BEANS024/Item-Speed-Control-in-Conveyor-Systems-/3D Printed Conveyor/STL Files/Motor Prime Mover Key couple.STL

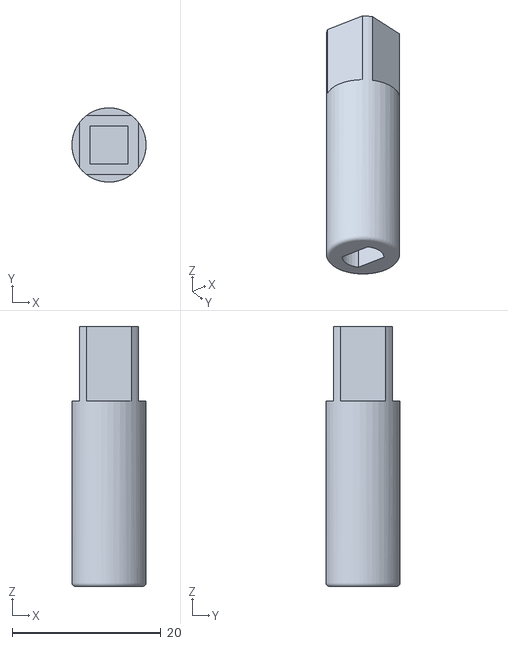
[picture p59: CAD file, 2026-04-25]
3D Printed Conveyor/STL Files/Motor Prime Mover Key couple.STL
10.0 x 10.00 x 35.0
