BEANS024/Item-Speed-Control-in-Conveyor-Systems-/sensor mount.STL

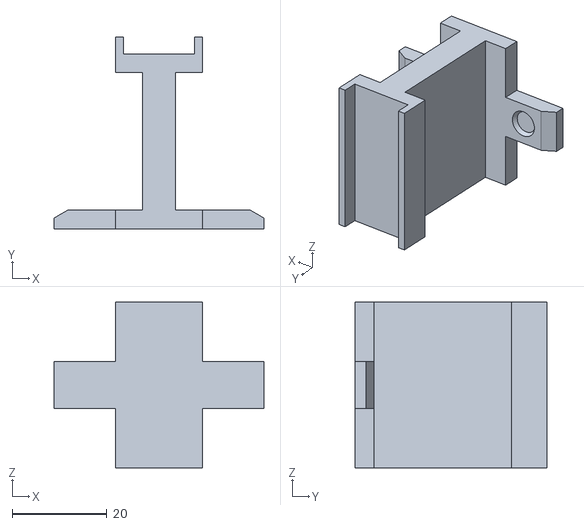
[picture p60: CAD file, 2026-05-06]
sensor mount.STL
44.4 x 40.5 x 35.0
