BEANS024/Item-Speed-Control-in-Conveyor-Systems-/3D Printed Conveyor/Frame /Conveyor Corner Frame with Motor Coupling slot.SLDPRT

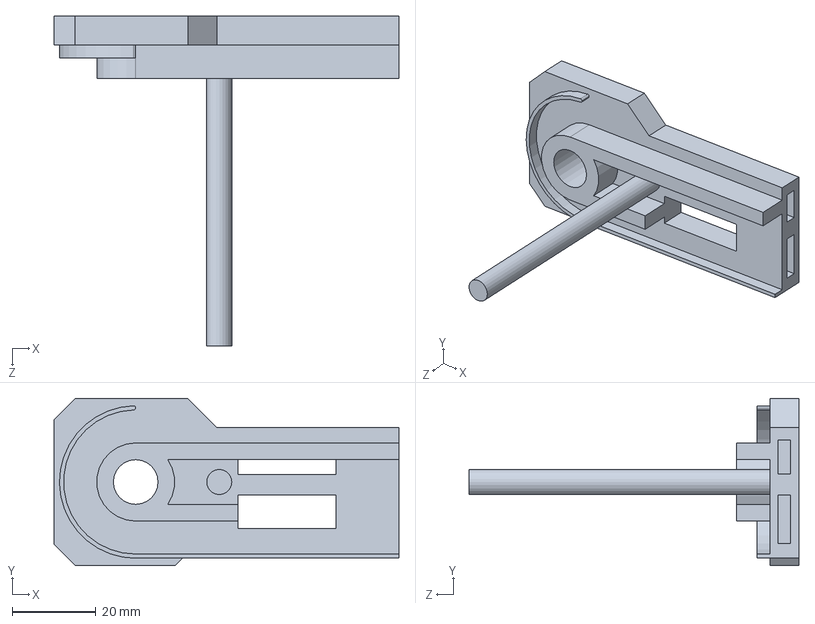
[picture p61: CAD file, 2026-04-25]
3D Printed Conveyor/Frame /Conveyor Corner Frame with Motor Coupling slot.SLDPRT
82.5 x 40.0 x 79.0 mm
