BEANS024/Item-Speed-Control-in-Conveyor-Systems-/belt bulk print x14.SLDPRT

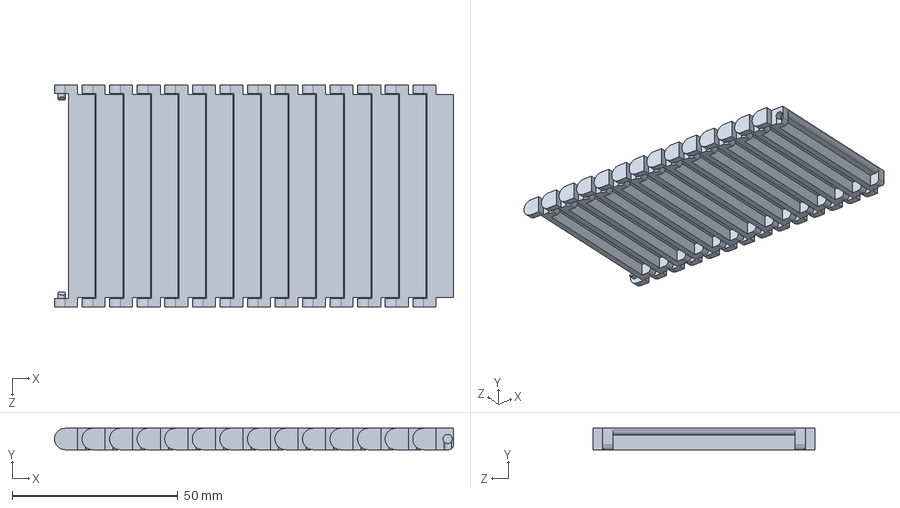
[picture p62: CAD file, 2026-04-25]
belt bulk print x14.SLDPRT
120.5 x 6.50 x 67.0 mm
