BEANS024/Item-Speed-Control-in-Conveyor-Systems-/3D Printed Conveyor/Electro-Mechanical design/MotorGear01.SLDPRT

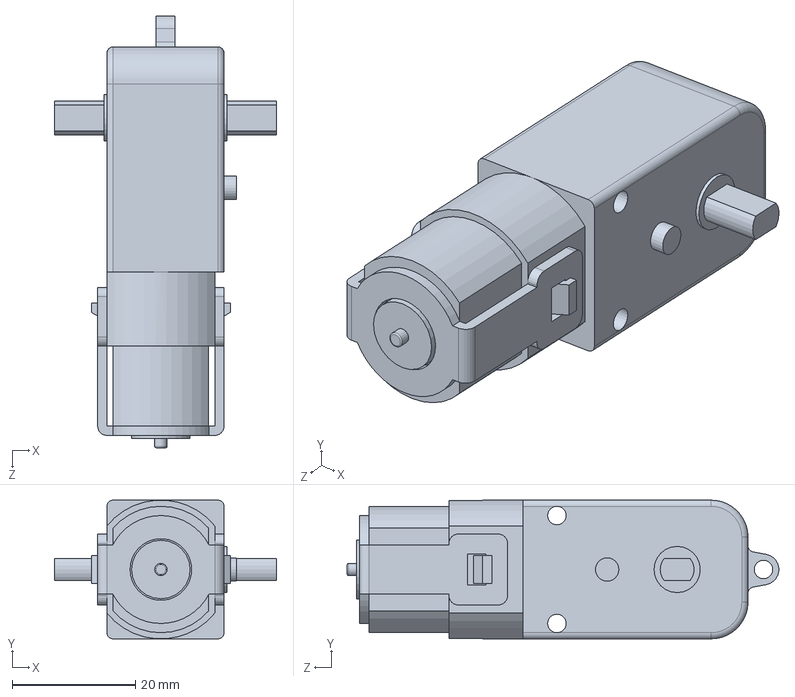
[picture p63: CAD file, 2026-04-23]
3D Printed Conveyor/Electro-Mechanical design/MotorGear01.SLDPRT
36.0 x 22.5 x 70.0 mm
