BEANS024/Item-Speed-Control-in-Conveyor-Systems-/3D Printed Conveyor/Frame /Conveyor frame corner male 2.SLDPRT

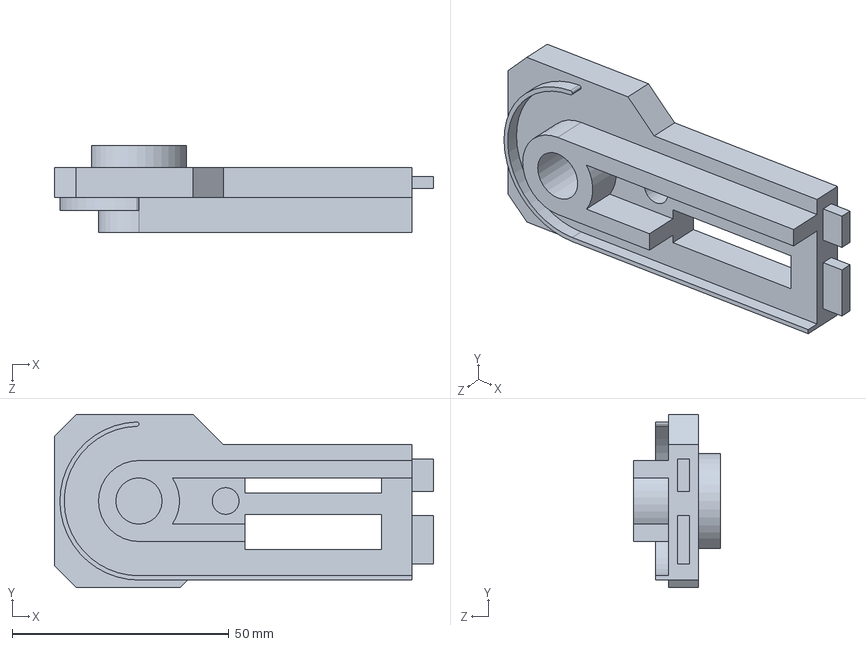
[picture p64: CAD file, 2026-04-25]
3D Printed Conveyor/Frame /Conveyor frame corner male 2.SLDPRT
87.5 x 40.0 x 20.0 mm
