BEANS024/Item-Speed-Control-in-Conveyor-Systems-/test belt 2.SLDPRT

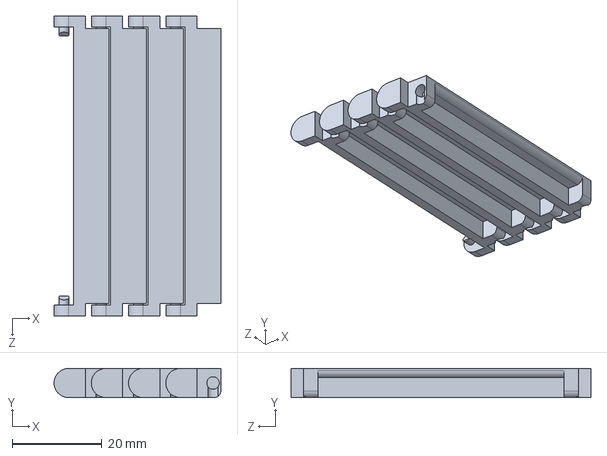
[picture p65: CAD file, 2026-04-25]
test belt 2.SLDPRT
37.3 x 6.50 x 67.0 mm
