BEANS024/Item-Speed-Control-in-Conveyor-Systems-/3D Printed Conveyor/Frame /DC Motor Chassis Cover.SLDPRT

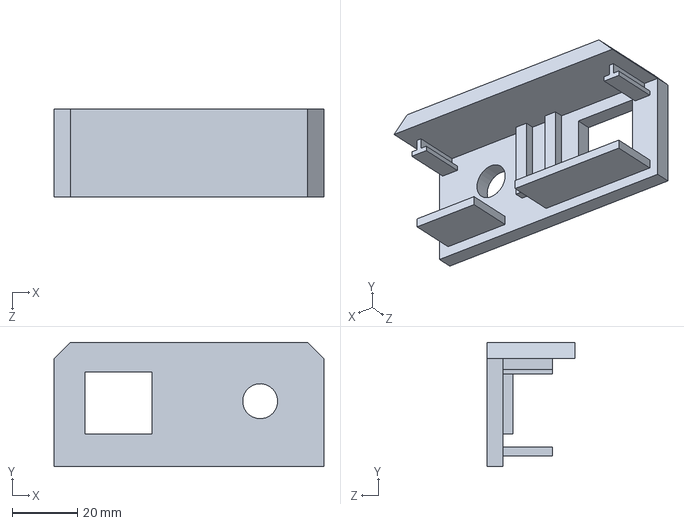
[picture p66: CAD file, 2026-04-25]
3D Printed Conveyor/Frame /DC Motor Chassis Cover.SLDPRT
82.5 x 38.0 x 27.0 mm
