BEANS024/Item-Speed-Control-in-Conveyor-Systems-/belt bulk print x28.SLDPRT

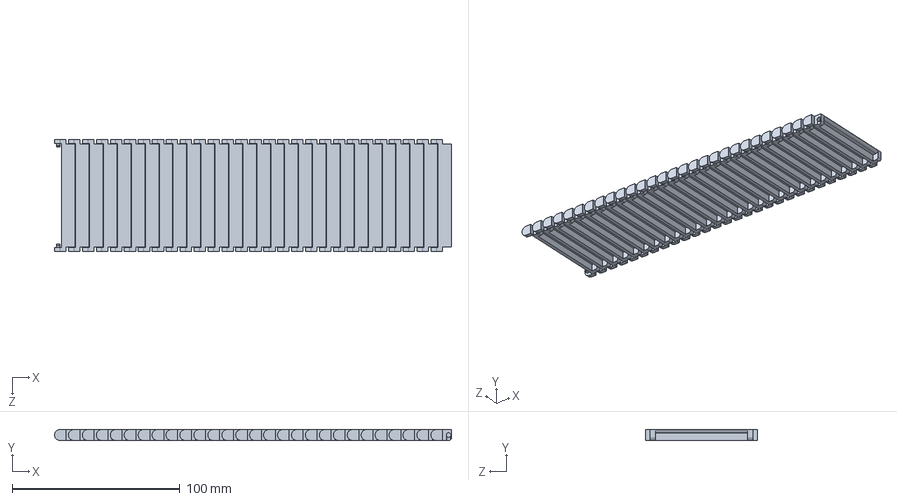
[picture p67: CAD file, 2026-04-25]
belt bulk print x28.SLDPRT
236.9 x 6.50 x 67.0 mm
