BEANS024/Item-Speed-Control-in-Conveyor-Systems-/3D Printed Conveyor/Frame /Conveyor Frame corner female 1.SLDPRT

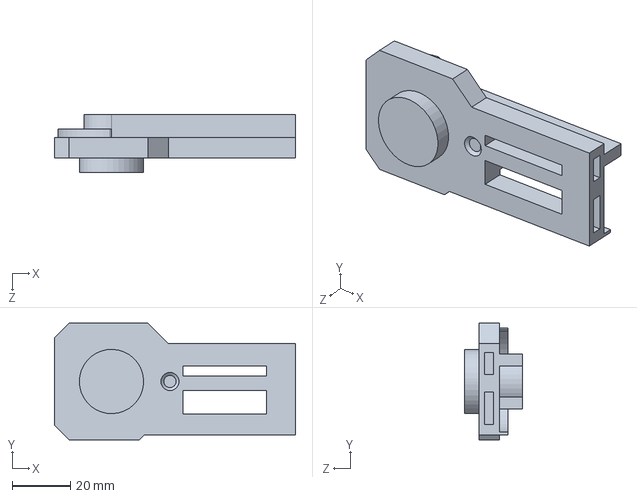
[picture p68: CAD file, 2026-04-25]
3D Printed Conveyor/Frame /Conveyor Frame corner female 1.SLDPRT
82.5 x 40.0 x 20.0 mm
