BEANS024/Item-Speed-Control-in-Conveyor-Systems-/375 ml Australian can RED.SLDASM

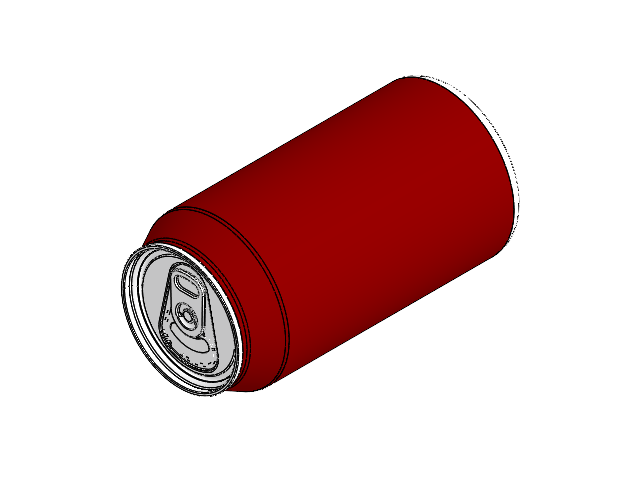
[picture p69: CAD file, 2026-04-23]
375 ml Australian can RED.SLDASM
Can.step
Ring.step
